borgel/sympetrum-v3/Hardware/Badge/release/Release V2/gerbers-pdf/Sympetrum-V3 FF3-In3.Cu.pdf

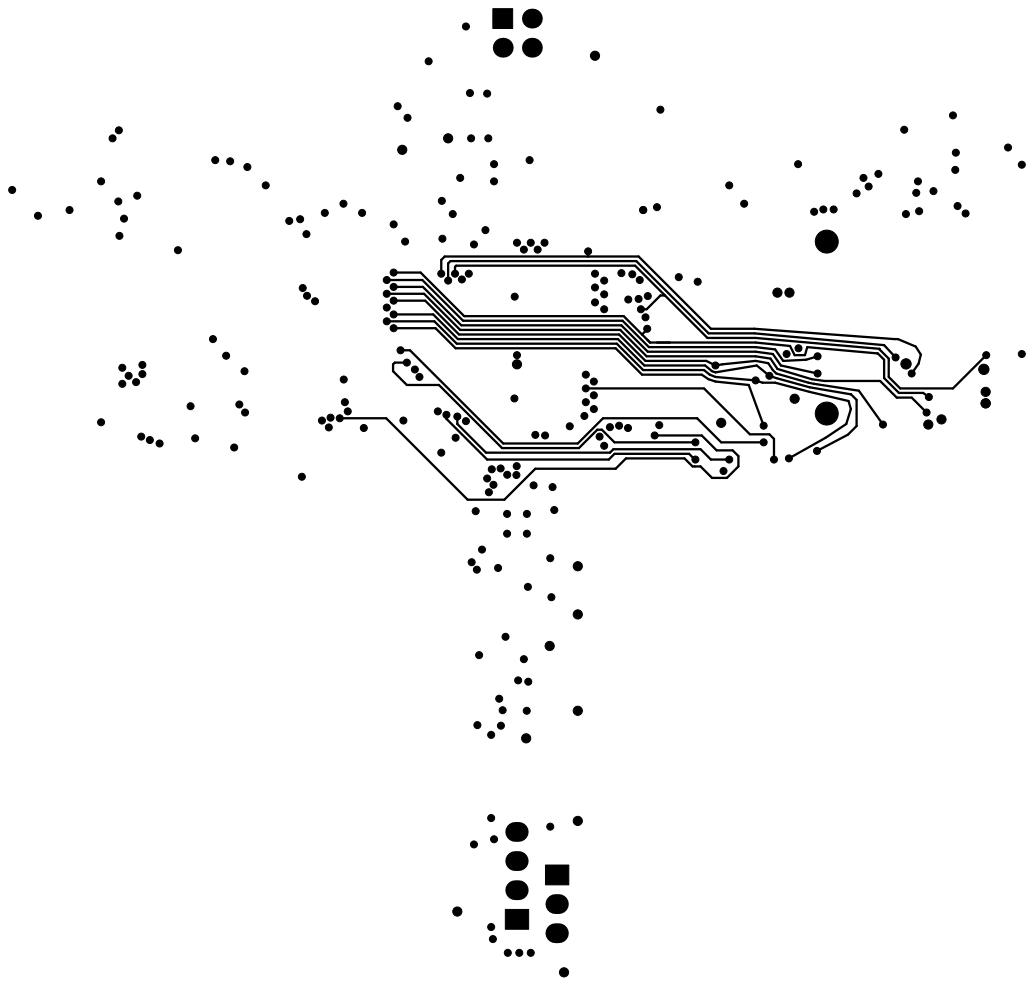
[picture p19: page 1]
