borgel/sympetrum-v3/Hardware/Badge/release/Release V2/gerbers-pdf/Sympetrum-V3 FF3-In4.Cu.pdf

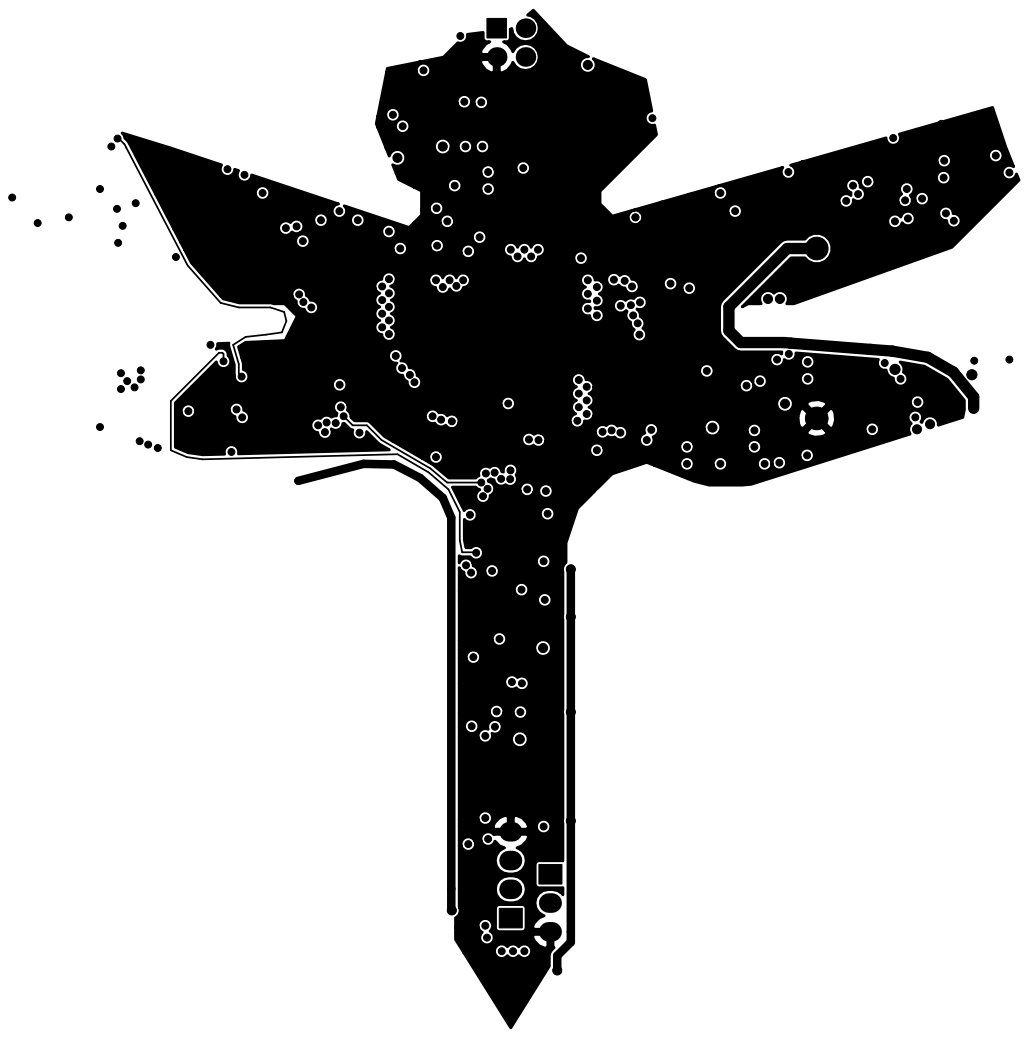
[picture p20: page 1]
