borgel/sympetrum-v3/Documentation/LED Mapping.pdf

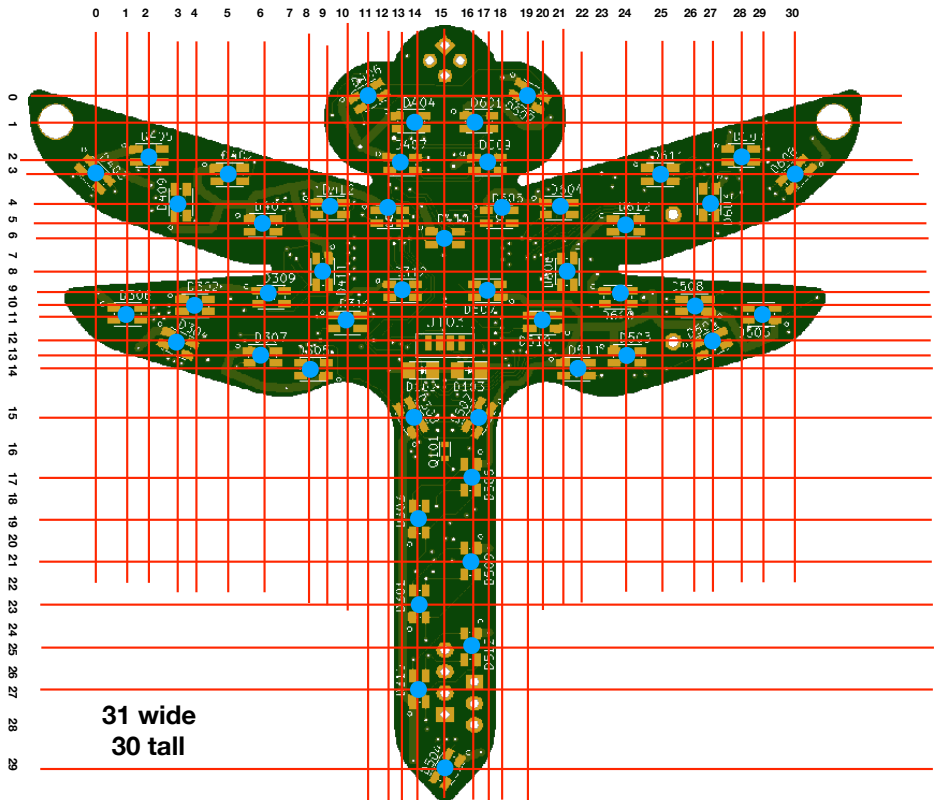
[picture p21: page 1]
31 wide 30 tall

5

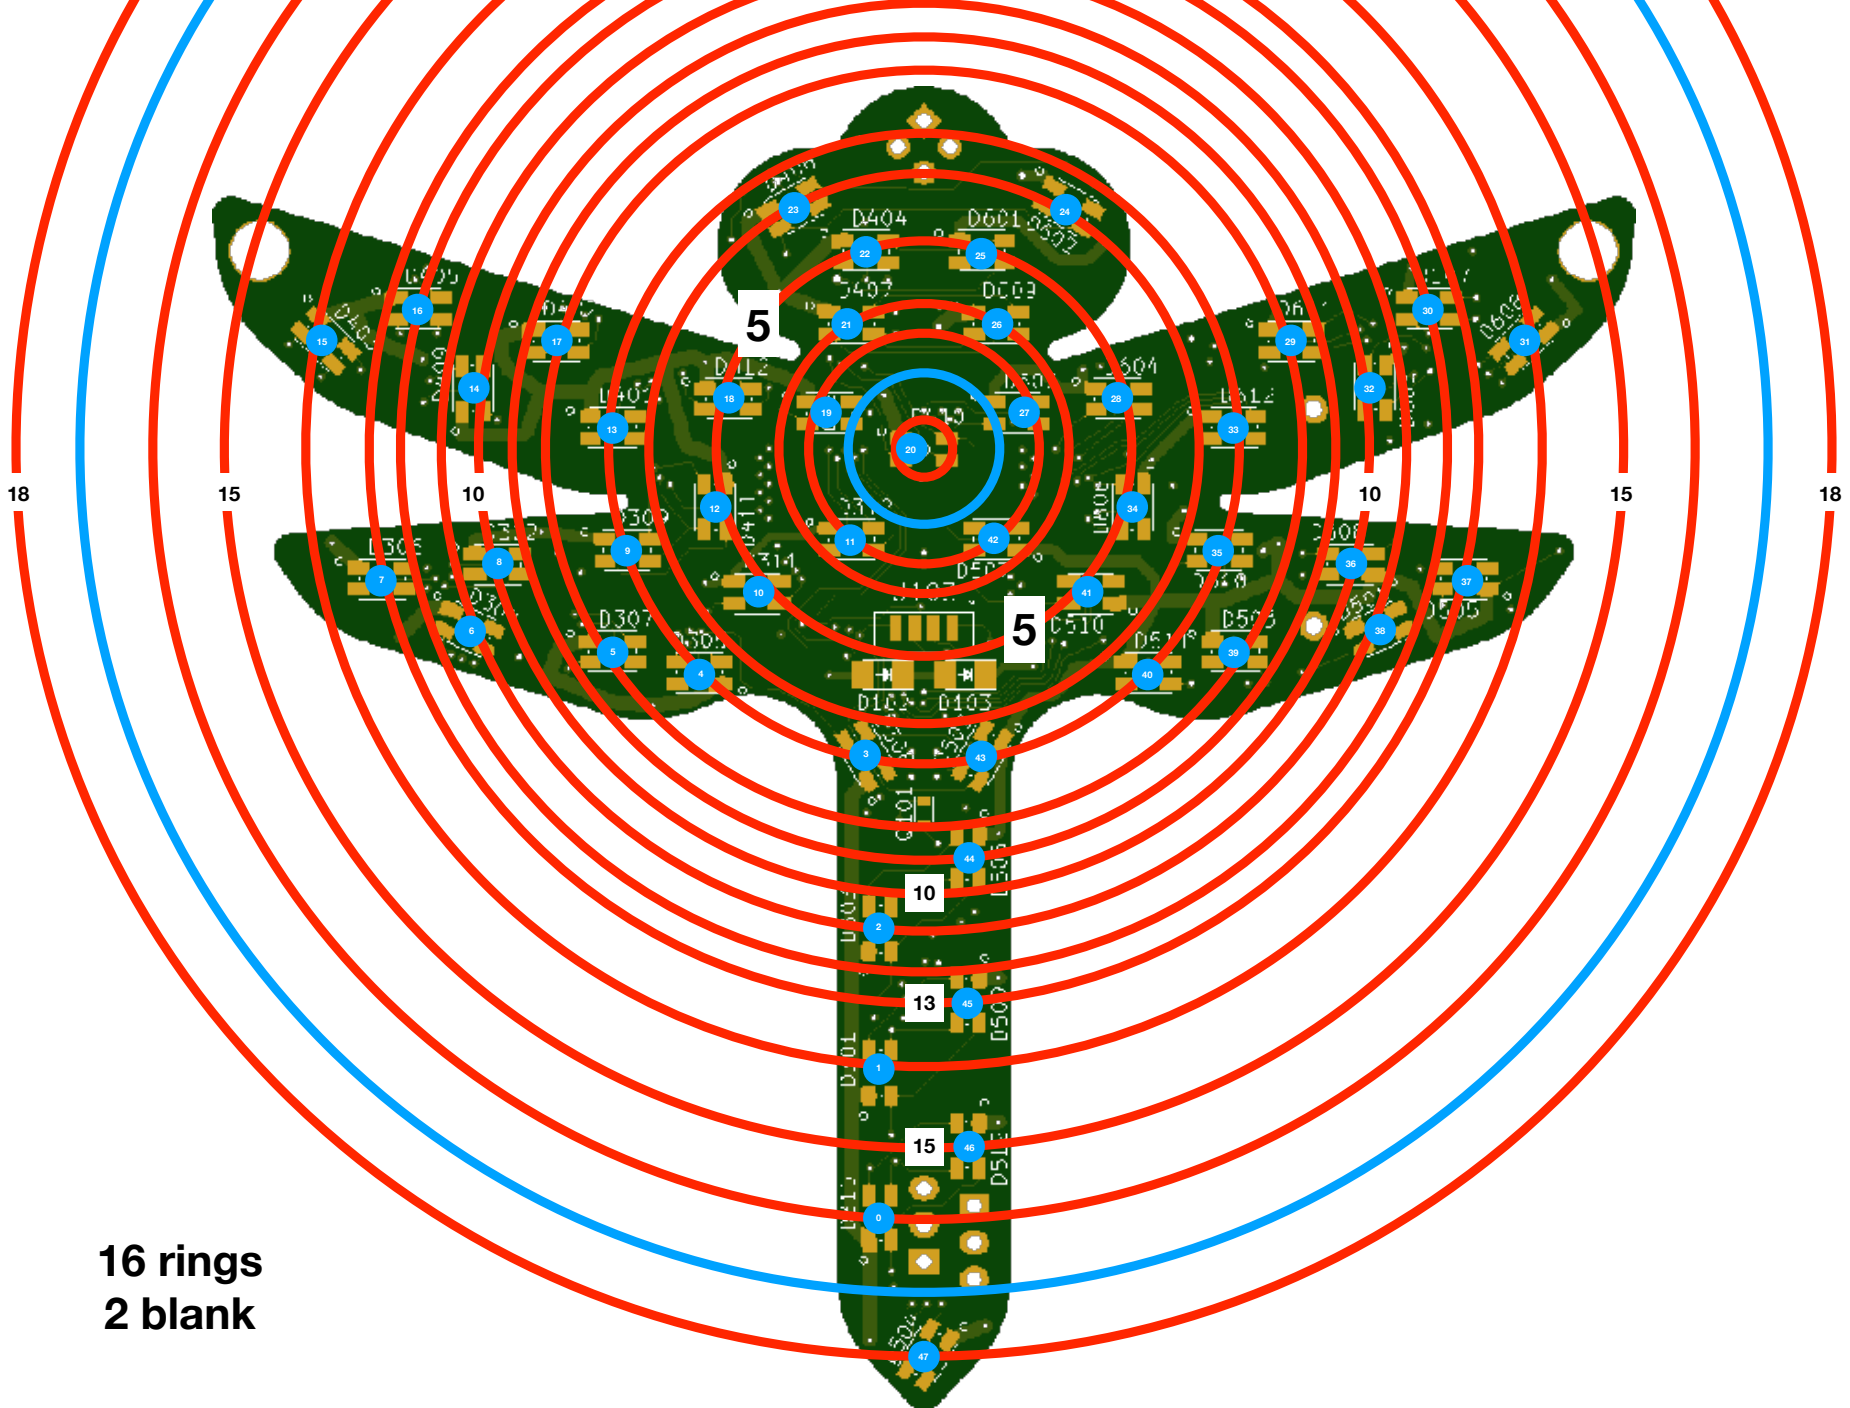
[picture p22: page 2]
16 rings 2 blank
